ravi6/TurnTable/Amp.kicad_sch

## KiCad design Amp.kicad_sch (2025-08-03)

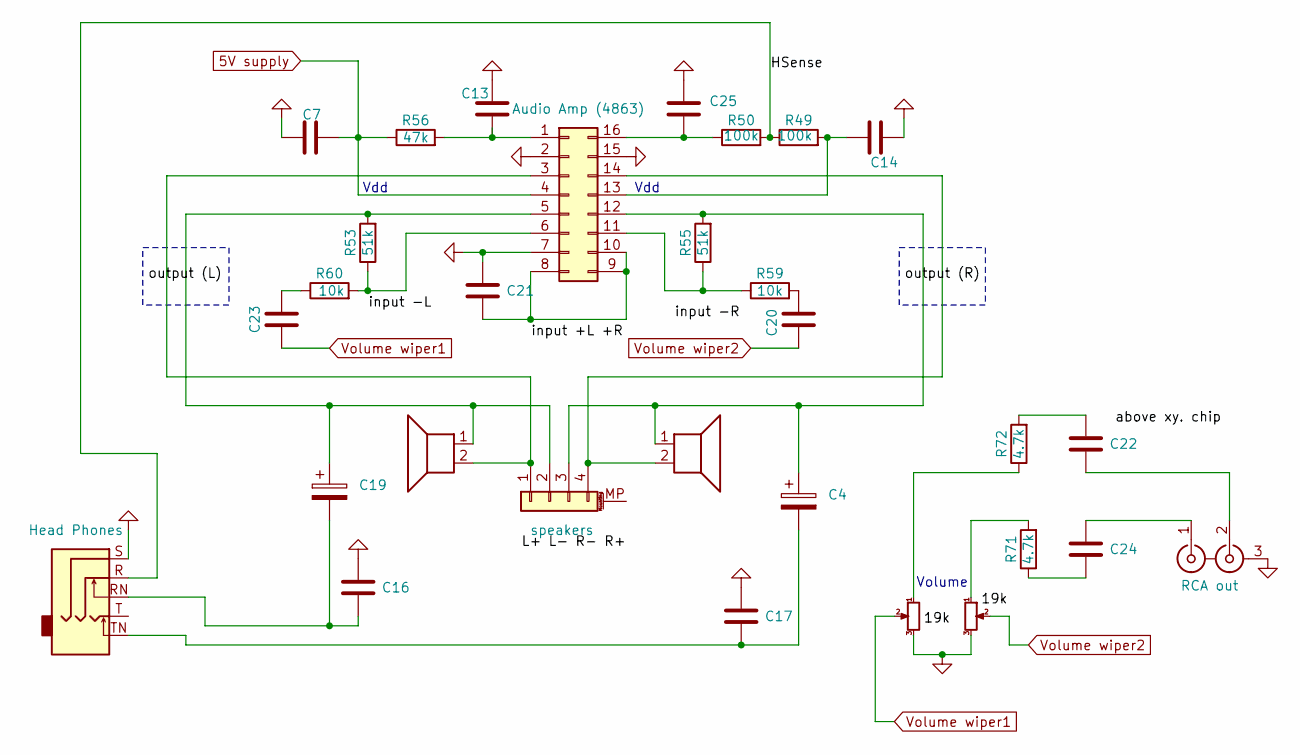
[picture p11: schematic Amp.kicad_sch]

Parts:
C4, C19: C_Polarized
C7, C13, C14, C16, C17, C20, C21, C22, C23, C24, C25: C
LS1: Speaker
R49, R50: 100k
R53, R55: 51k
R56: 47k
R59, R60: 10k
R71, R72: 4.7k
RV1: R_Potentiometer_Small

Connections:
5V supply: C7.1, R56.1
GND: C7.2, C13.1, C14.2, C16.2, C17.2, C21.2, C25.2, RV1.3
HSense: R49.1, R50.2
unnamed: C4.1, R55.2
unnamed: C13.2, R56.2
unnamed: C14.1, R49.2
unnamed: C16.1, C19.2
unnamed: C4.2, C17.1
unnamed: C19.1, LS1.1, R53.2
unnamed: C20.1, R59.2
unnamed: C22.2, R72.2
unnamed: C23.2, R60.1
unnamed: C24.1, R71.1
unnamed: C25.1, R50.1
unnamed: R53.1, R60.2
unnamed: R55.1, R59.1
unnamed: R71.2, RV1.1
Volume wiper1: C23.1
Volume wiper2: C20.2, RV1.2

Notes on the sheet:
Vdd
Volume
