ravi6/TurnTable/Mux.kicad_sch

## KiCad design Mux.kicad_sch (2025-08-03)

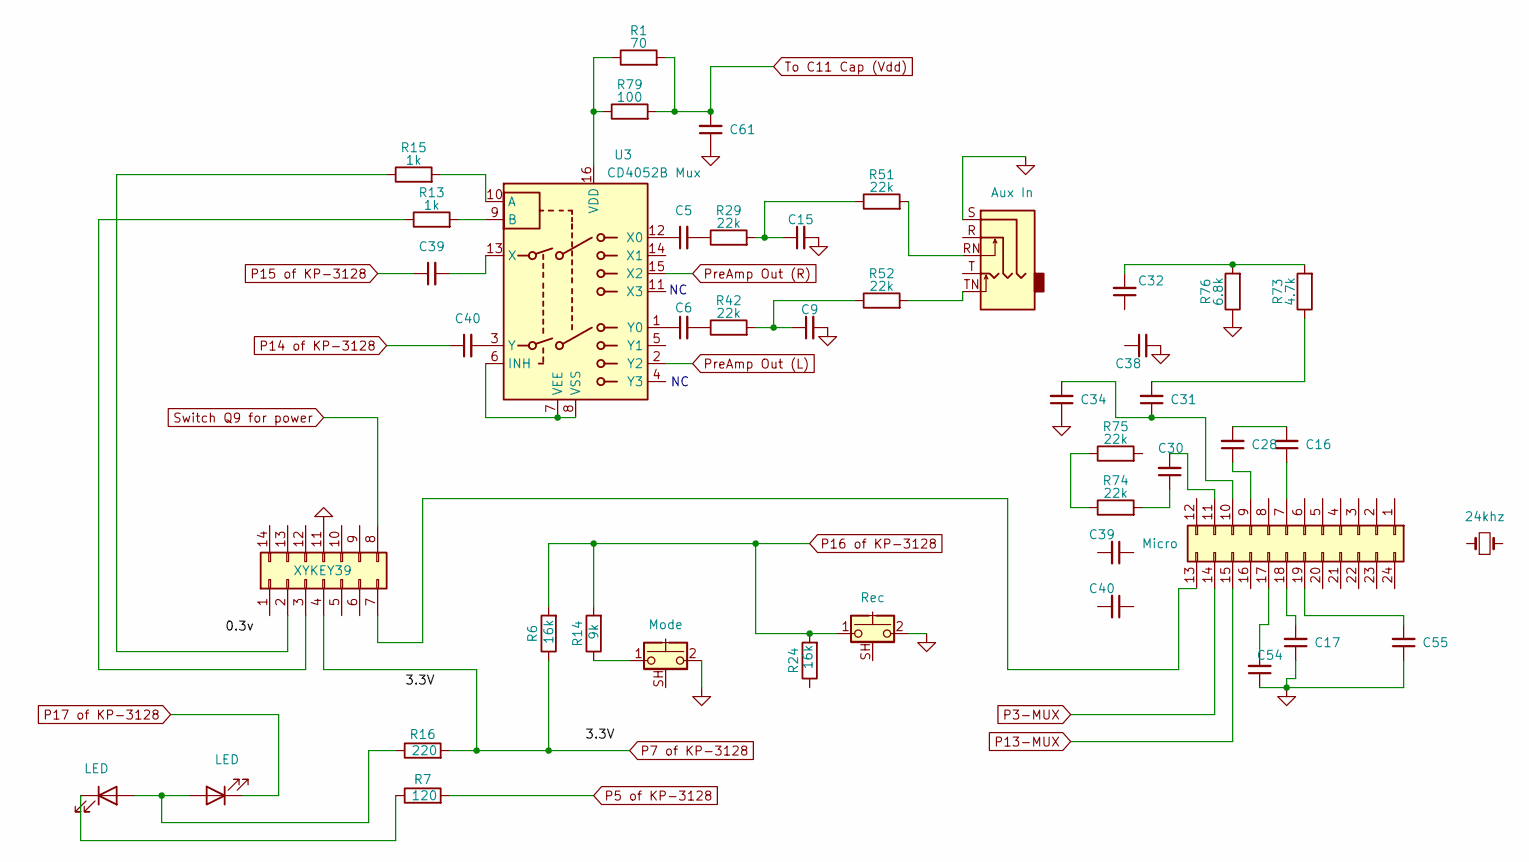
[picture p12: schematic Mux.kicad_sch]

Parts:
C5, C6, C9, C15, C16, C17, C28, C30, C31, C32, C34, C38, C39, C40, C54, C55, C61: C_Small
J1: Aux In
J2: XYKEY39
R1: 70
R6, R24: 16k
R7: 120
R13, R15: 1k
R14: 9k
R16: 220
R29, R42, R51, R52, R74, R75: 22k
R73: 4.7k
R76: 6.8k
R79: 100
SW3: Rec
SW4: Mode
U3: CD4052B Mux

Connections:
GND: C9.2, C15.2, C17.1, C34.1, C38.2, C54.1, C55.1, C61.1, J1.S, J2.11, R76.1, SW3.2, SW4.2
unnamed: C5.1, U3.12 (X0)
unnamed: C5.2, R29.1
unnamed: C6.1, U3.1 (Y0)
unnamed: C6.2, R42.1
unnamed: C9.1, R42.2, R52.1
unnamed: C15.1, R29.2, R51.1
unnamed: C16.2, C28.2
unnamed: C30.1, R74.2
unnamed: C31.1, C34.2
unnamed: C31.2, R73.1
unnamed: C32.2, R73.2, R76.2
unnamed: C39.2, U3.13 (X)
unnamed: C40.2, U3.3 (Y)
unnamed: J1.RN, R51.2
unnamed: J1.TN, R52.2
unnamed: J2.2, R15.1
unnamed: J2.3, R13.1
unnamed: R1.1, R79.1, U3.16 (VDD)
unnamed: R13.2, U3.9 (B)
unnamed: R14.1, SW4.1
unnamed: R15.2, U3.10 (A)
unnamed: R74.1, R75.1
unnamed: U3.6 (INH), U3.7 (VEE), U3.8 (VSS)
P5 of KP-3128: R7.2
P7 of KP-3128: J2.4, R6.1, R16.2
P14 of KP-3128: C40.1
P15 of KP-3128: C39.1
P16 of KP-3128: R6.2, R14.2, R24.2, SW3.1
PreAmp Out (L): U3.2 (Y2)
PreAmp Out (R): U3.15 (X2)
Switch Q9 for power: J2.8
To C11 Cap (Vdd): C61.2, R1.2, R79.2
