ravi6/TurnTable/PreAmp.kicad_sch

## KiCad design PreAmp.kicad_sch (2025-08-03)

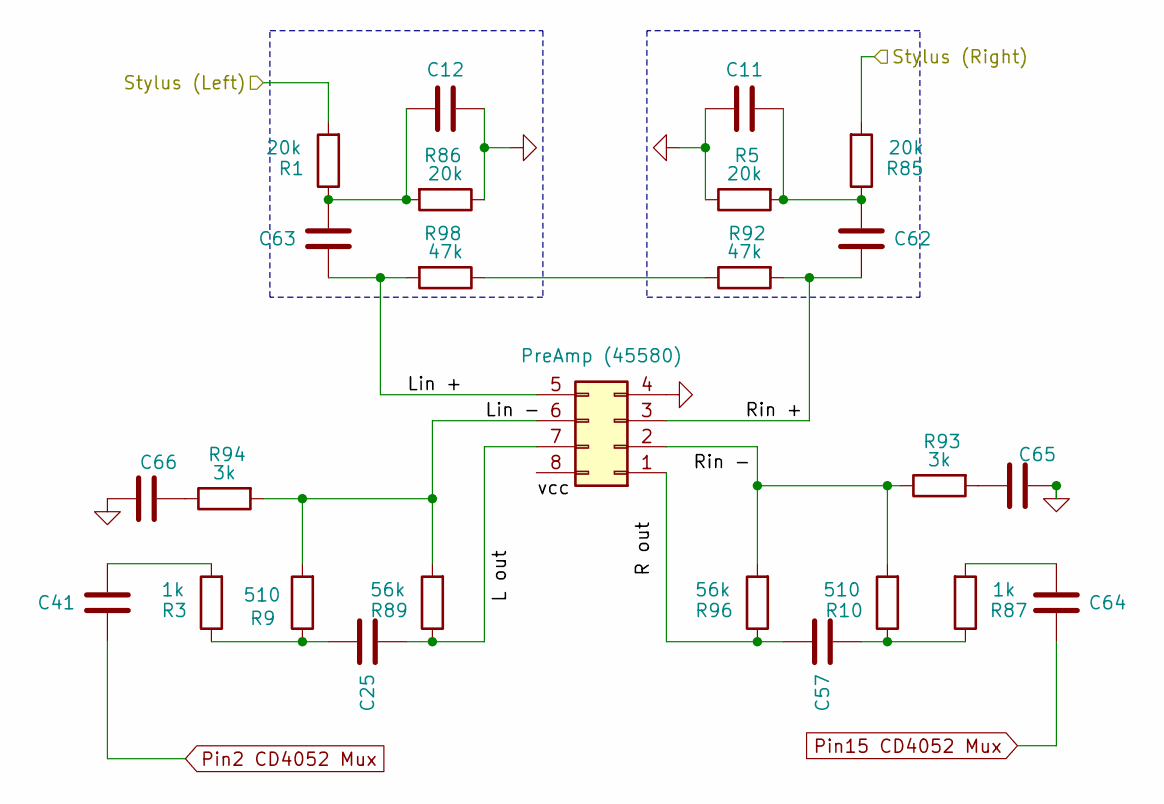
[picture p13: schematic PreAmp.kicad_sch]

Parts:
C11, C12, C25, C41, C57, C62, C63, C64, C65, C66: C
J3: PreAmp (45580)
R1, R5, R85, R86: 20k
R3, R87: 1k
R9, R10: 510
R89, R96: 56k
R92, R98: 47k
R93, R94: 3k

Connections:
GND: C11.1, C12.1, C65.1, C66.2, J3.4, R5.1, R86.1
Lin +: C63.1, J3.5, R98.2
Lin -: J3.6, R9.2, R89.2, R94.2
unnamed: C11.2, C62.2, R5.2, R85.1
unnamed: C12.2, C63.2, R1.1, R86.2
unnamed: C25.1, J3.7, R89.1
unnamed: C25.2, R3.1, R9.1
unnamed: C41.1, R3.2
unnamed: C57.1, J3.1, R96.1
unnamed: C57.2, R10.1, R87.1
unnamed: C64.1, R87.2
unnamed: C65.2, R93.2
unnamed: C66.1, R94.1
unnamed: J3.2, R10.2, R93.1, R96.2
unnamed: R92.1, R98.1
Pin2 CD4052 Mux: C41.2
Pin15 CD4052 Mux: C64.2
Rin +: C62.1, J3.3, R92.2
Stylus (Left): R1.2
Stylus (Right): R85.2
