ravi6/TurnTable/turntable.kicad_sch

## KiCad design turntable.kicad_sch (2025-08-03)

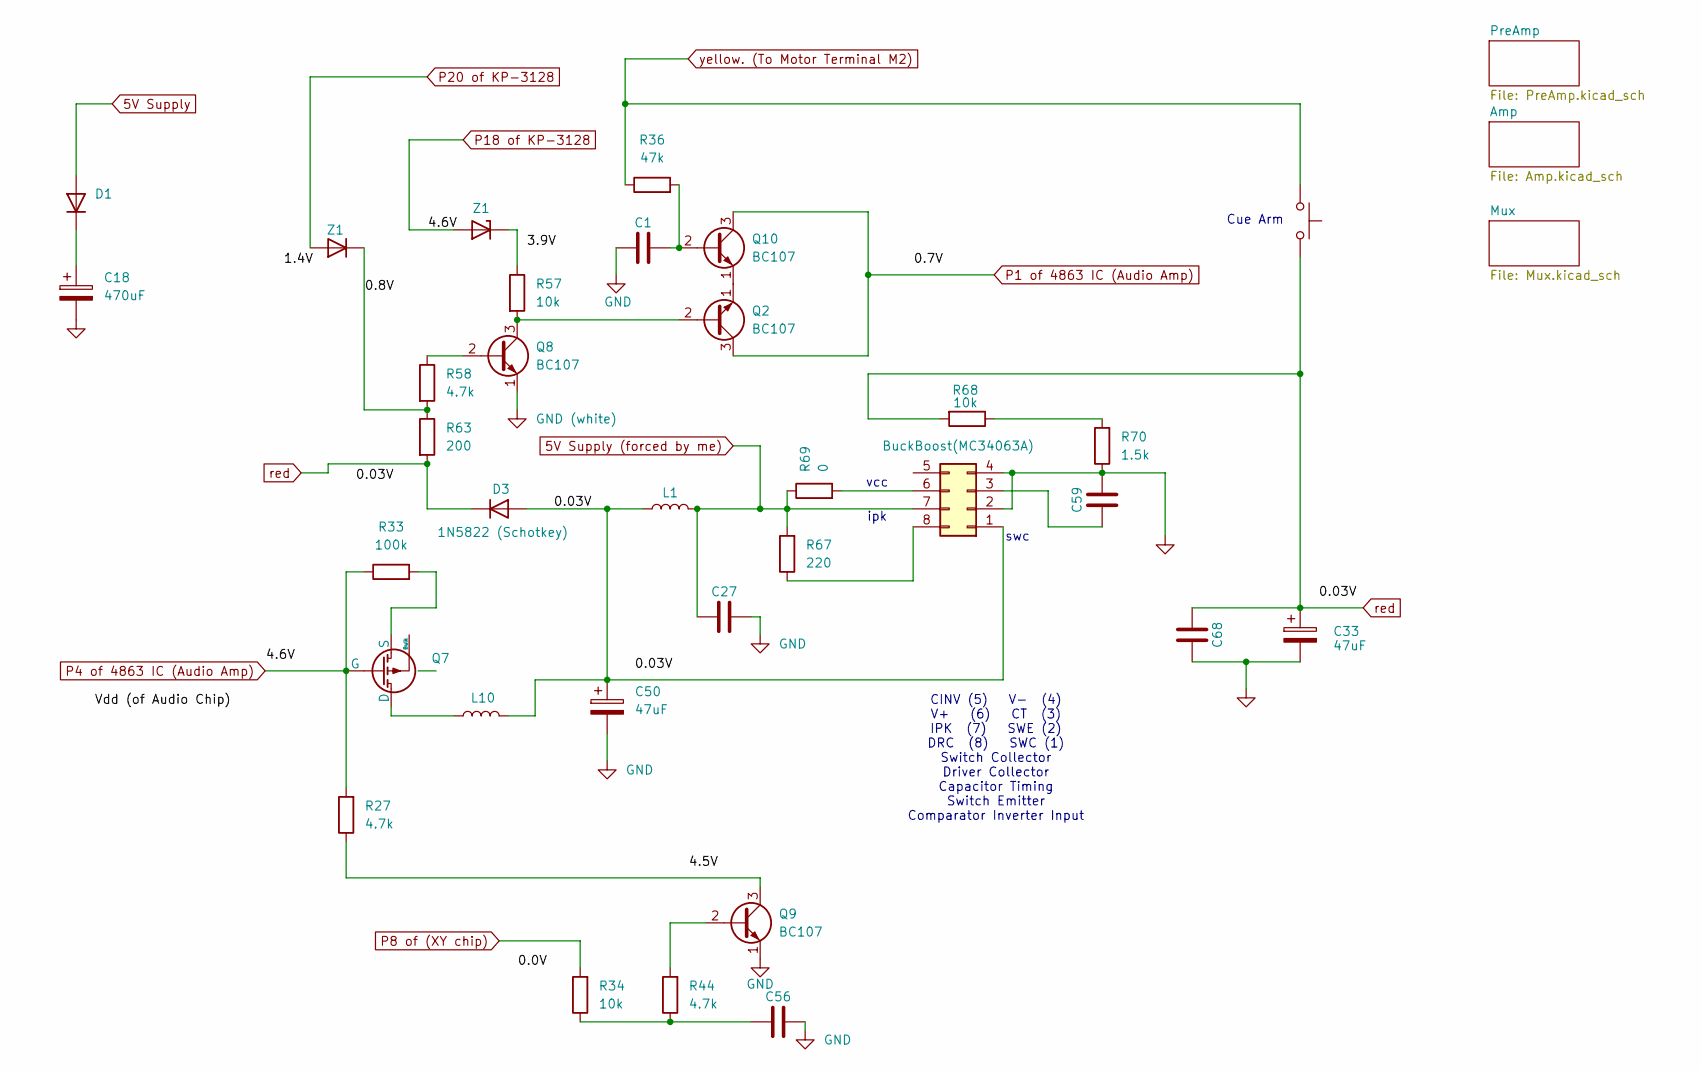
[picture p14: schematic turntable.kicad_sch]

Parts:
BuckBoost(MC34063A): Conn_02x04_Counter_Clockwise
C1, C27, C56, C59, C68: C
C18: 470uF
C33, C50: 47uF
D1: D
D3: 1N5822 (Schotkey)
L1, L10: L
Q2, Q8, Q9, Q10: BC107; TO-18-3
Q7: PMOS_Substrate
R27, R44, R58: 4.7k
R33: 100k
R34, R57, R68: 10k
R36: 47k
R63: 200
R67: 220
R69: 0
R70: 1.5k
SW2: SW_Push
Z1: D

Connections:
0.03V: BuckBoost(MC34063A).1, C50.1, D3.2 (A), L1.1, L10.2
0.8V: R58.2, R63.1, Z1.1 (K)
5V Supply: D1.2 (A)
5V Supply (forced by me): BuckBoost(MC34063A).7, C27.1, L1.2, R67.2, R69.1
GND: C1.1, C18.2, C27.2, C50.2, C56.2, Q9.1 (E)
GND (white): BuckBoost(MC34063A).2, BuckBoost(MC34063A).4, C33.2, C59.2, C68.2, Q8.1 (E), R70.1
unnamed: BuckBoost(MC34063A).3, C59.1
unnamed: BuckBoost(MC34063A).6, R69.2
unnamed: BuckBoost(MC34063A).8, R67.1
unnamed: C1.2, Q10.2 (B), R36.2
unnamed: C18.1, D1.1 (K)
unnamed: C56.1, R34.1, R44.1
unnamed: L10.1, Q7.1 (D)
unnamed: Q2.2 (B), Q8.3 (C), R57.2
unnamed: Q7.3 (S), R33.2
unnamed: Q8.2 (B), R58.1
unnamed: Q9.2 (B), R44.2
unnamed: Q9.3 (C), R27.1
unnamed: Q2.1 (E), Q10.1 (E)
unnamed: R57.1, Z1.1 (K)
unnamed: R68.1, R70.2
P1 of 4863 IC (Audio Amp): Q2.3 (C), Q10.3 (C)
P4 of 4863 IC (Audio Amp): Q7.2 (G), R27.2, R33.1
P8 of (XY chip): R34.2
P18 of KP-3128: Z1.2 (A)
P20 of KP-3128: Z1.2 (A)
red: C33.1, C68.1, D3.1 (K), R63.2, R68.2, SW2.2
yellow. (To Motor Terminal M2): R36.1, SW2.1

Notes on the sheet:
vcc
Cue Arm
ipk
swc
CINV (5) V- (4) V+ (6) CT (3) IPK (7) SWE (2) DRC (8) SWC (1) Switch Collector Driver Collector Capacitor Timing Switch Emitter Comparator Inverter Input
